rafkhan/lowstepper/lowstepper_firmware/src/pot_input.cpp

#include <Arduino.h>

#include "pot_input.h"

PotInput::PotInput(int pinNum) {
  this->pin = pinNum;
  this->value = 0;
}

PotInput::~PotInput() {}

void PotInput::init() {
  pinMode(this->pin, INPUT);
}

void PotInput::scan() {
  this->value = (double) analogRead(this->pin);
}

double PotInput::getValue() {
  return this->value;
}
