rafkhan/lowstepper/lowstepper_daisy_firmware/lowstepper/ui/pins.h

#ifndef PINS_H
#define PINS_H

// REFER TO KICAD REV1 SCHEMATIC

#define PIN_EOC_A 0
#define PIN_EOC_B 1
#define PIN_DAC_OUT_A 0
#define PIN_DAC_OUT_B 0

#define PIN_LED_A_R 3
#define PIN_LED_A_G 4
#define PIN_LED_A_B 5
#define PIN_LED_B_R 6
#define PIN_LED_B_G 9
#define PIN_LED_B_B 10

#define PIN_CLK_IN_A 24
#define PIN_TRIG_IN_A 25
#define PIN_RESET_IN_A 26
#define PIN_CLK_IN_B 27
#define PIN_TRIG_IN_B 28
#define PIN_RESET_IN_B 29

#define PIN_CLK_IN_A_SENSE 30
#define PIN_TRIG_IN_A_SENSE 31
#define PIN_RESET_IN_A_SENSE 32
#define PIN_CLK_IN_B_SENSE 15
#define PIN_TRIG_IN_B_SENSE 16
#define PIN_RESET_IN_B_SENSE 17

#define PIN_RATE_POT_A 33
#define PIN_MORPH_POT_A 34
#define PIN_CHUNK_POT_A 35
#define PIN_RATE_CV_A 36
#define PIN_MORPH_CV_A 37
#define PIN_CHUNK_CV_A 38

#define PIN_RATE_POT_B 23
#define PIN_MORPH_POT_B 22
#define PIN_CHUNK_POT_B 21
#define PIN_RATE_CV_B 20
#define PIN_MORPH_CV_B 19
#define PIN_CHUNK_CV_B 18

#endif
