rafkhan/lowstepper/lowstepper_daisy_firmware/lowstepper/util.h

#ifndef UTIL_H 
#define UTIL_H

#include <cstdint>

#ifndef HALF_PI
#define HALF_PI 1.5707963268f
#endif

#ifndef PI
#define PI 3.14159265359f
#endif

#ifndef TWO_PI
#define TWO_PI 6.28318530718f
#endif

#ifndef min
#define min(a,b)  (((a) < (b)) ? (a) : (b))
#endif

uint16_t mapFFII(float x, float in_min, float in_max, int out_min, int out_max);
float mapFFFF(float x, float in_min, float in_max, float out_min, float out_max);
float combinePotAndCv(float potValue, float cvValue, bool applyThreshold = false);

struct LowStepperOutput {
  bool eocGateHigh;
  float cvOutput; // -1 to 1
  float phase;
};

#endif
