rafkhan/lowstepper/lowstepper_daisy_firmware/lowstepper/ui/GateOut.h

#ifndef TRIG_OUT_H
#define TRIG_OUT_H

#include <stdint.h>
#include "../modes/BaseMode.h"

class GateOut : public TrigWriter
{
private:
  int pin;
  bool isHigh;
  uint32_t startTime;
  uint32_t endTime;

  void setHigh(void);
  void setLow(void);
public:
  GateOut(int pinNum);
  ~GateOut();

  void init(void);
  virtual void setHighForDuration(uint32_t currentTime, uint32_t duration);
  virtual void sendTrig(uint32_t currentTime);
  virtual void tick(uint32_t currentTime);
};

#endif
