rafkhan/lowstepper/lowstepper_daisy_firmware/lowstepper/ui/AnalogIn.h

#ifndef ANALOG_IN_IN 
#define ANALOG_IN_IN

class AnalogIn
{
private:
  int pin;
  int value;
public:
  AnalogIn(int pinNum);
  ~AnalogIn();

  void init(void);
  void scan(void);
  int getValue();
};

#endif
